LoehrLab/MMM_Duet_System/MMM_Duet_System_Software/images/switch.png

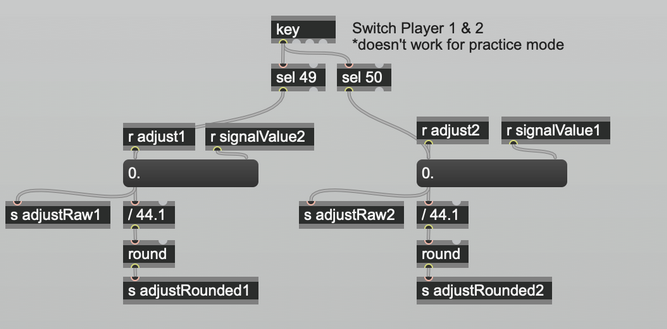
MMM_Duet_System_Software/images/switch.png
