LoehrLab/MMM_Duet_System/MMM_Duet_System_Software/MMM_Project/media/enlarged_road.png

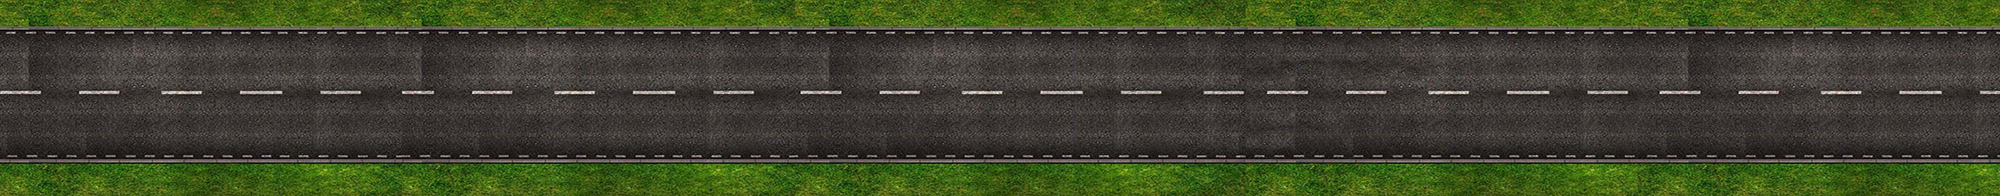
MMM_Duet_System_Software/MMM_Project/media/enlarged_road.png
