LoehrLab/MMM_Duet_System/MMM_Duet_System_Software/MMM_Project/media/Green_circle.png

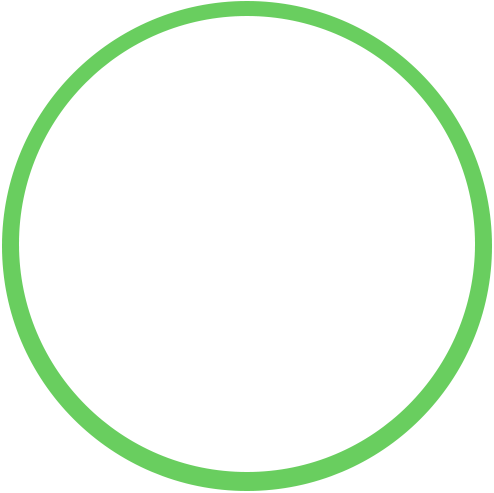
MMM_Duet_System_Software/MMM_Project/media/Green_circle.png
