LoehrLab/MMM_Duet_System/MMM_Duet_System_Software/MMM_Project/media/John_McCormack.jpg

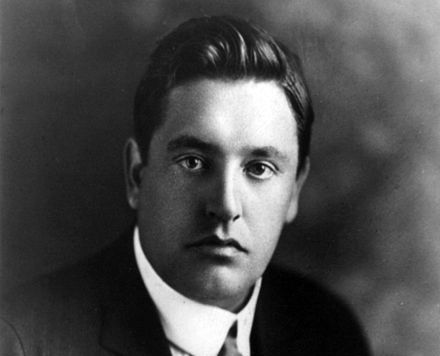
MMM_Duet_System_Software/MMM_Project/media/John_McCormack.jpg
