LoehrLab/MMM_Duet_System/MMM_Duet_System_Software/MMM_Project/media/tree-upside-down.png

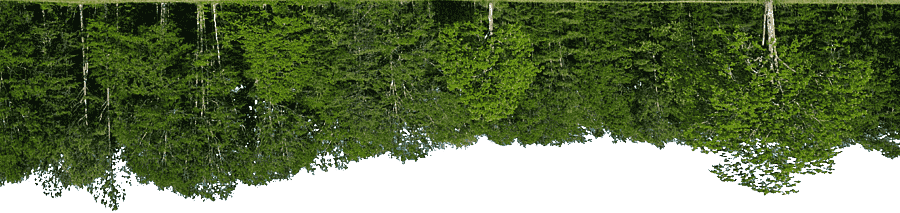
MMM_Duet_System_Software/MMM_Project/media/tree-upside-down.png
